juckettd/RaspberryPiCM4Handheld7Inch/Images/IMG_2084.jpg

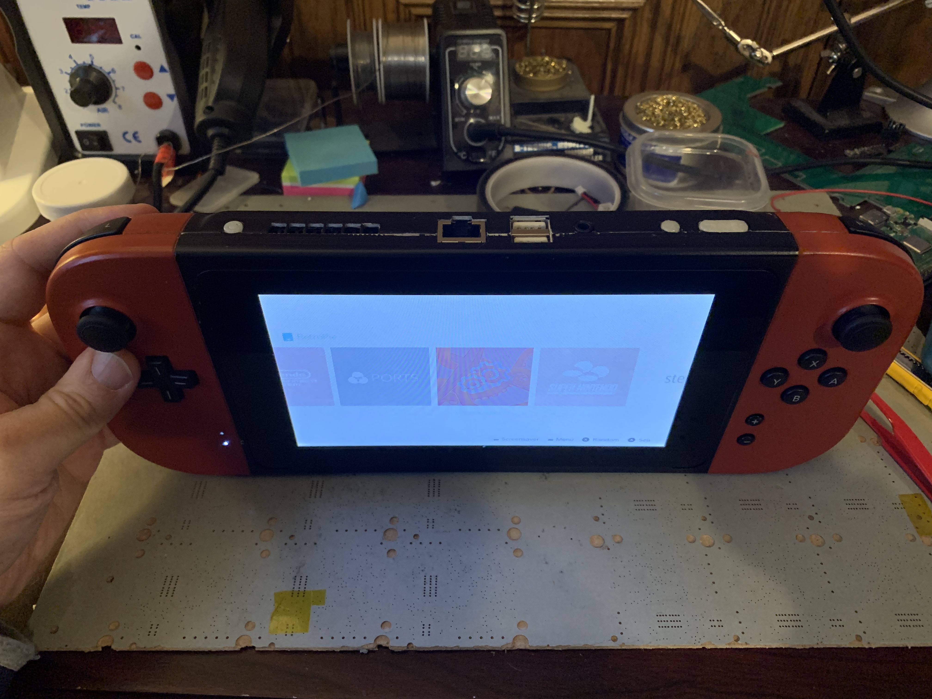
Images/IMG_2084.jpg
