juckettd/RaspberryPiCM4Handheld7Inch/Images/IMG_2085.jpg

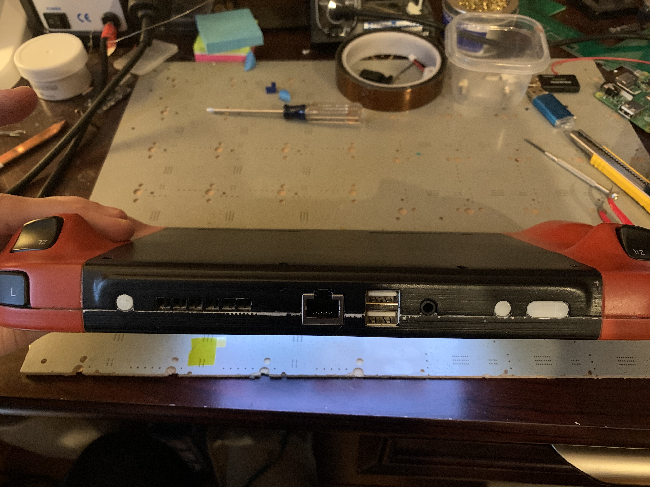
Images/IMG_2085.jpg
