juckettd/RaspberryPiCM4Handheld7Inch/Images/IMG_2086.jpg

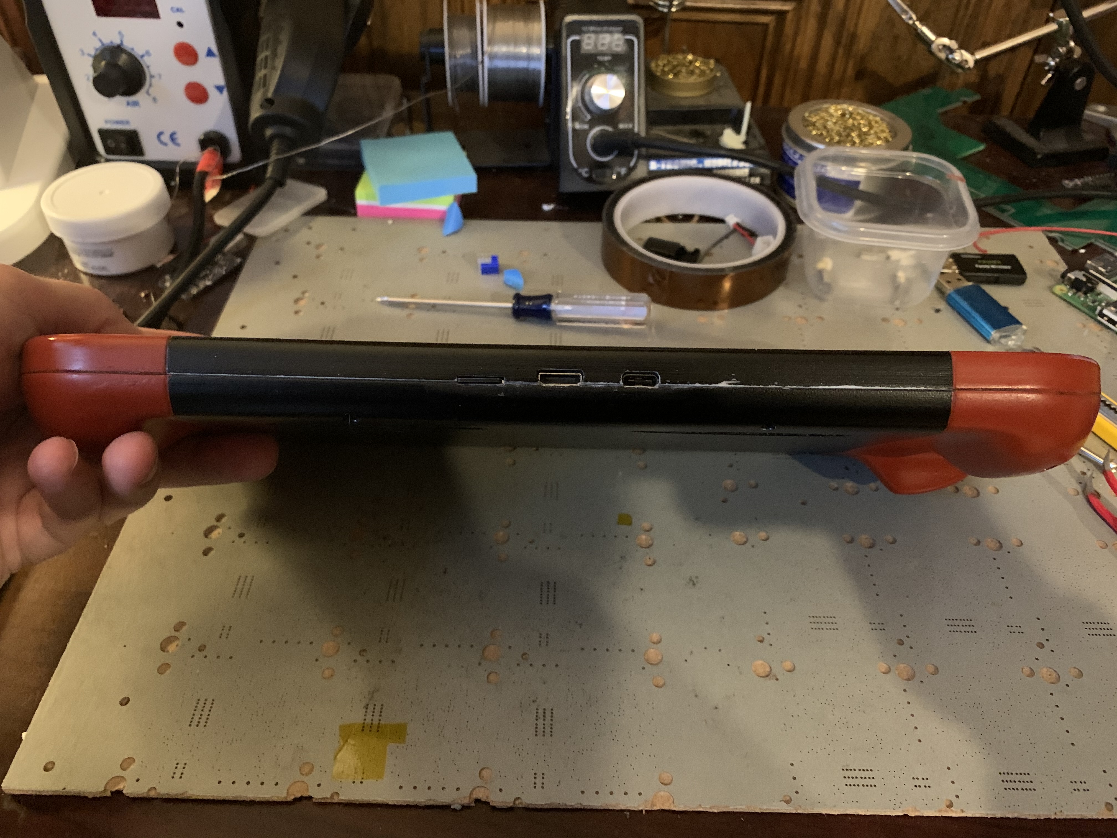
Images/IMG_2086.jpg
