juckettd/RaspberryPiCM4Handheld7Inch/Images/IMG_2087.jpg

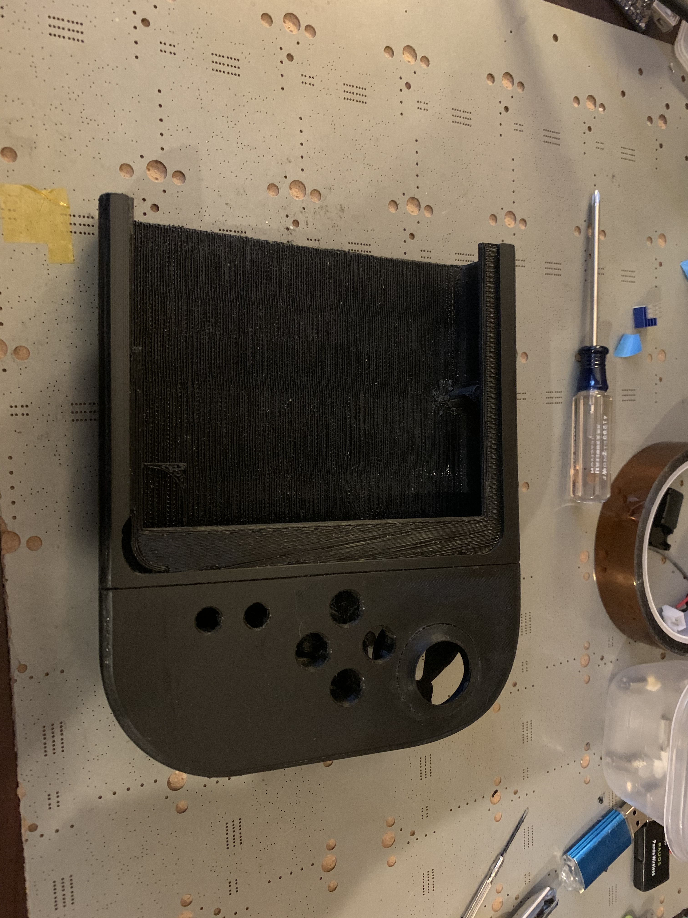
Images/IMG_2087.jpg
