juckettd/RaspberryPiCM4Handheld7Inch/Images/IMG_2089.jpg

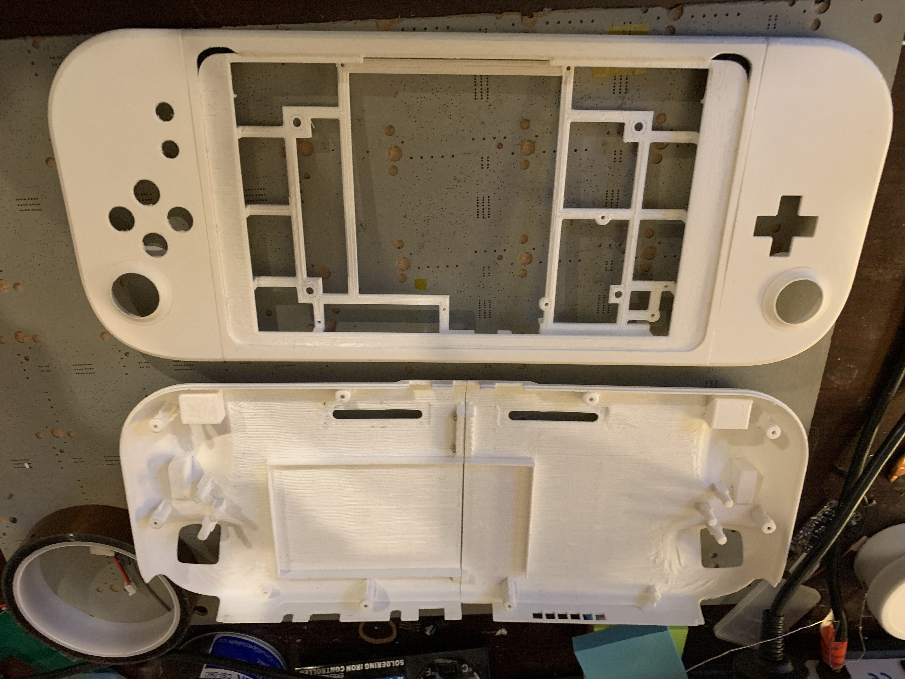
Images/IMG_2089.jpg
