juckettd/RaspberryPiCM4Handheld7Inch/Images/IMG_2090.jpg

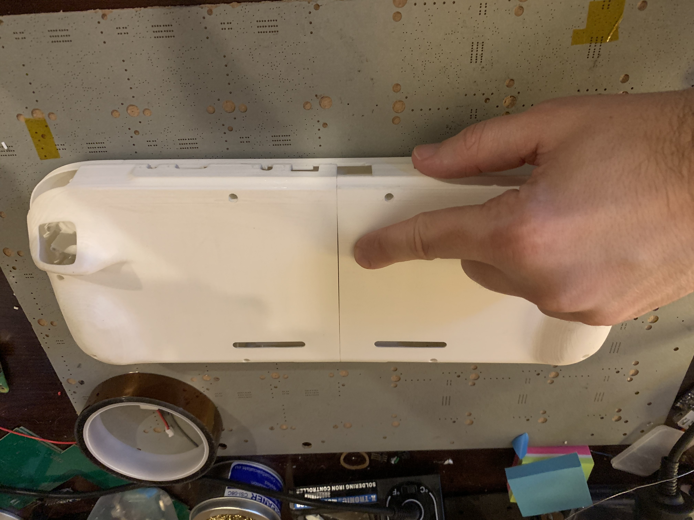
Images/IMG_2090.jpg
