juckettd/RaspberryPiCM4Handheld7Inch/Images/IMG_2092.jpg

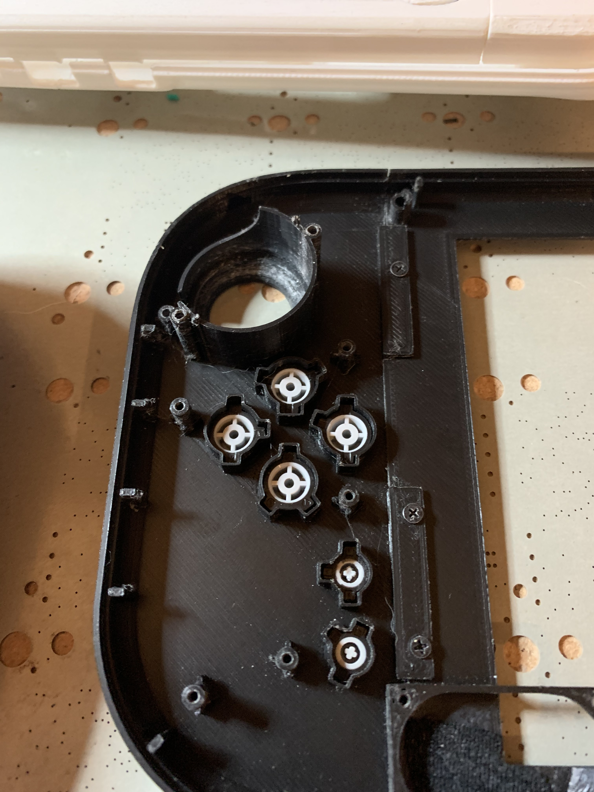
Images/IMG_2092.jpg
