juckettd/RaspberryPiCM4Handheld7Inch/Images/IMG_2093.jpg

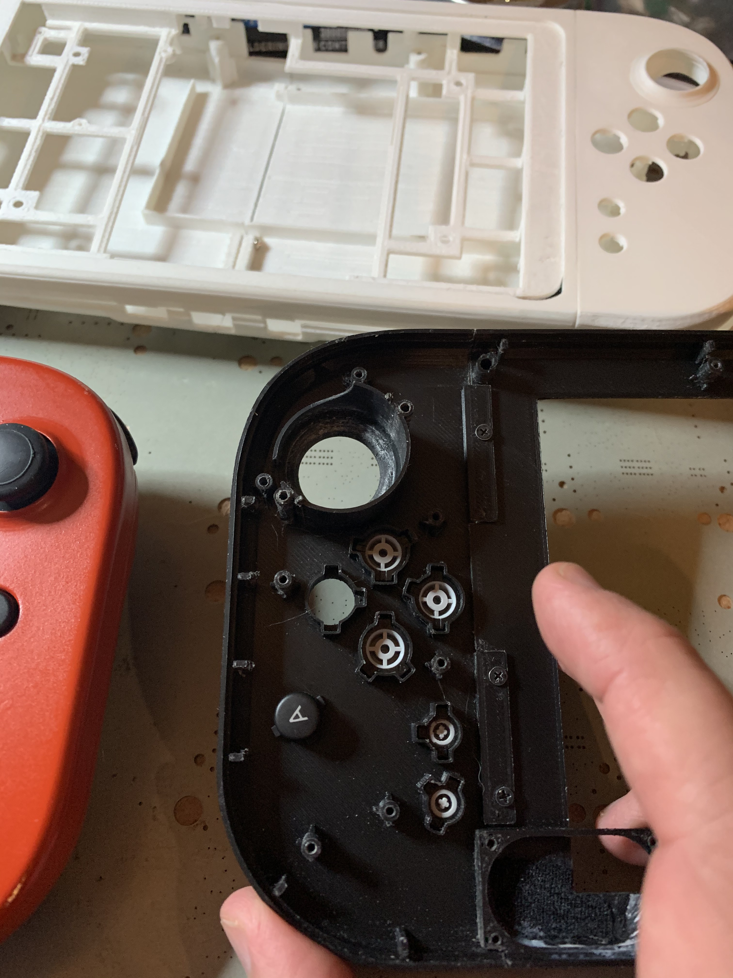
Images/IMG_2093.jpg
