juckettd/RaspberryPiCM4Handheld7Inch/Images/IMG_2094.jpg

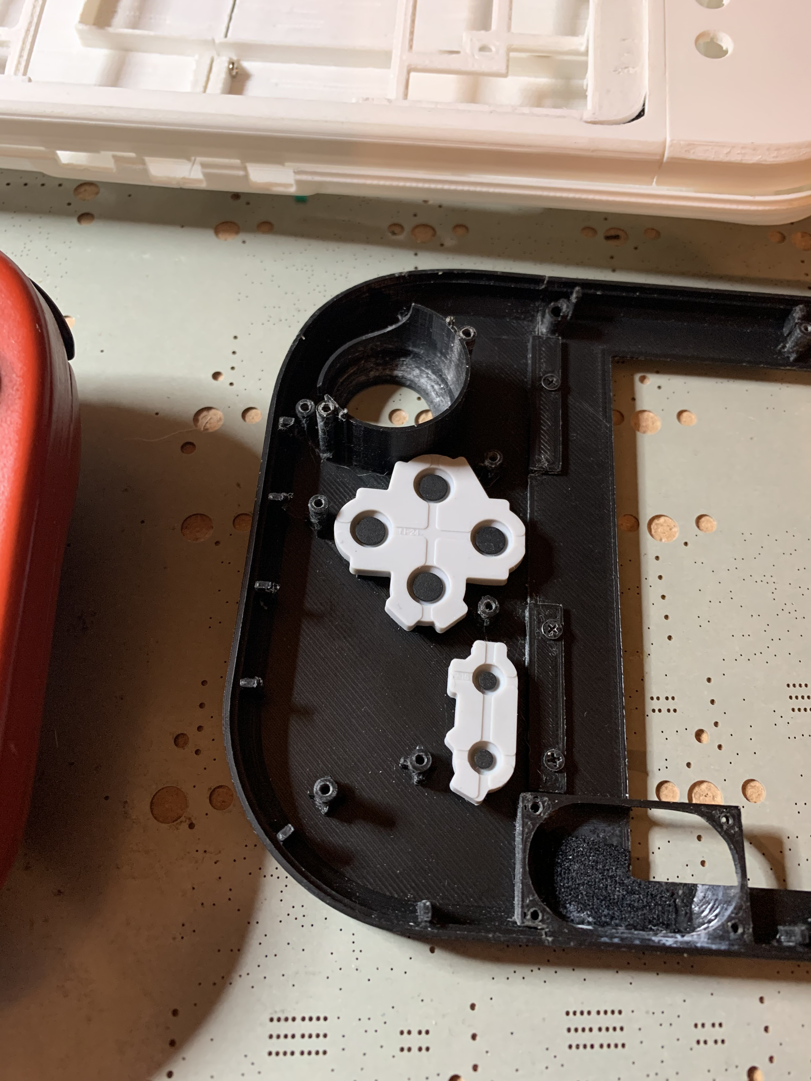
Images/IMG_2094.jpg
