juckettd/RaspberryPiCM4Handheld7Inch/Images/IMG_2095.jpg

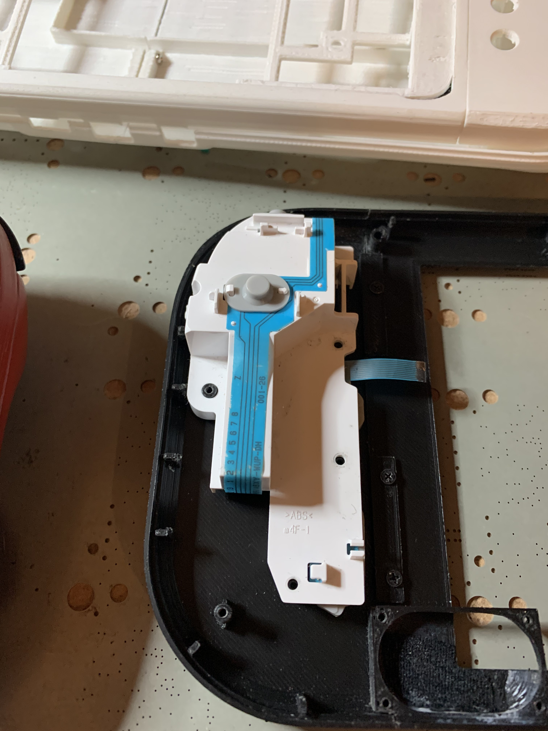
Images/IMG_2095.jpg
