juckettd/RaspberryPiCM4Handheld7Inch/Images/IMG_2096.jpg

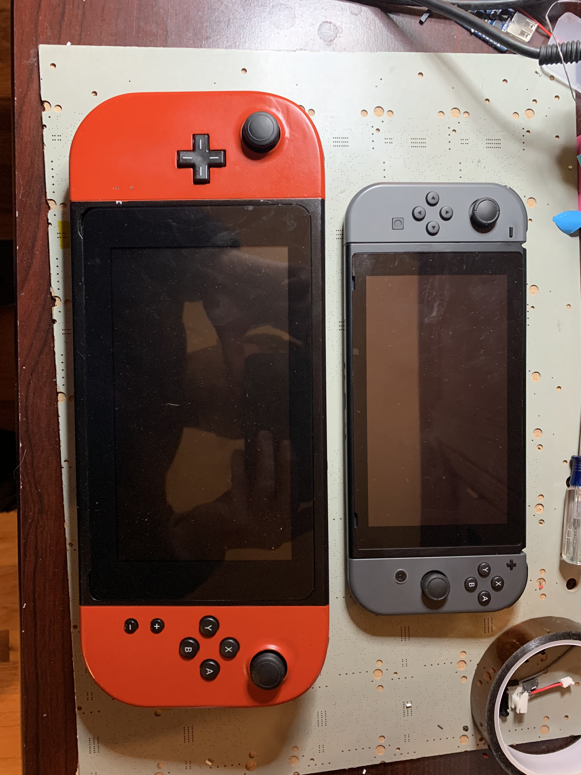
Images/IMG_2096.jpg
