juckettd/RaspberryPiCM4Handheld7Inch/Images/IMG_2108.jpg

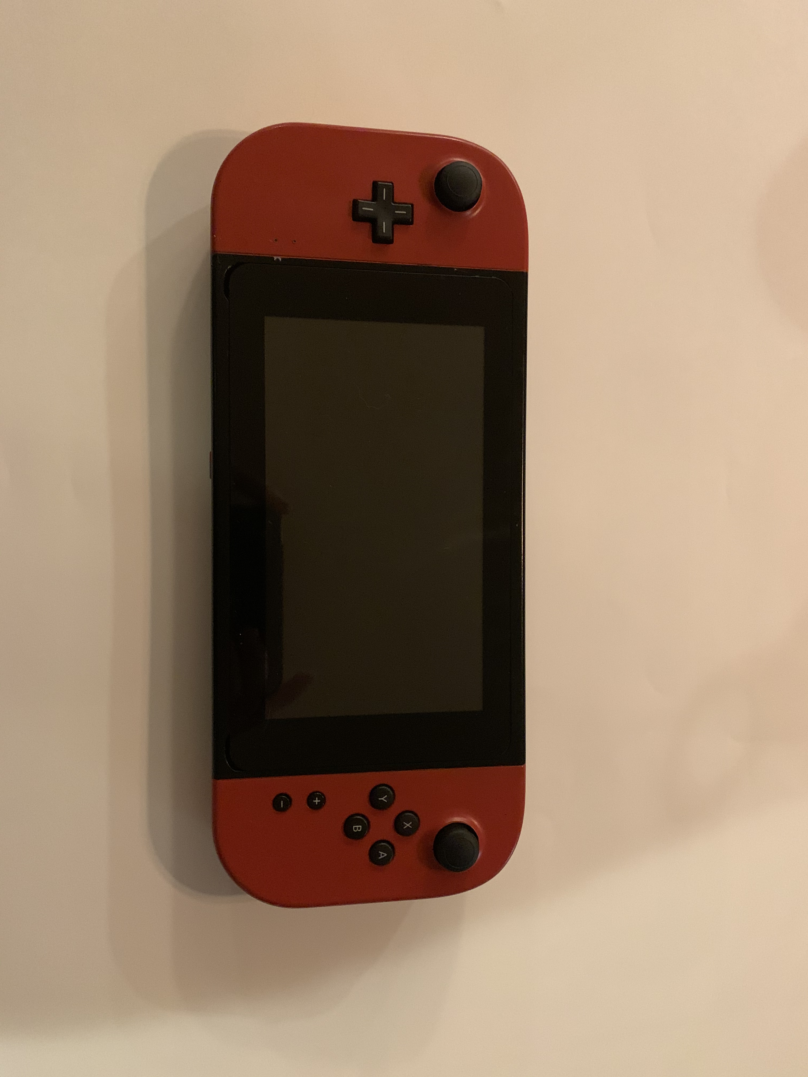
Images/IMG_2108.jpg
