juckettd/RaspberryPiCM4Handheld7Inch/Images/IMG_2109.jpg

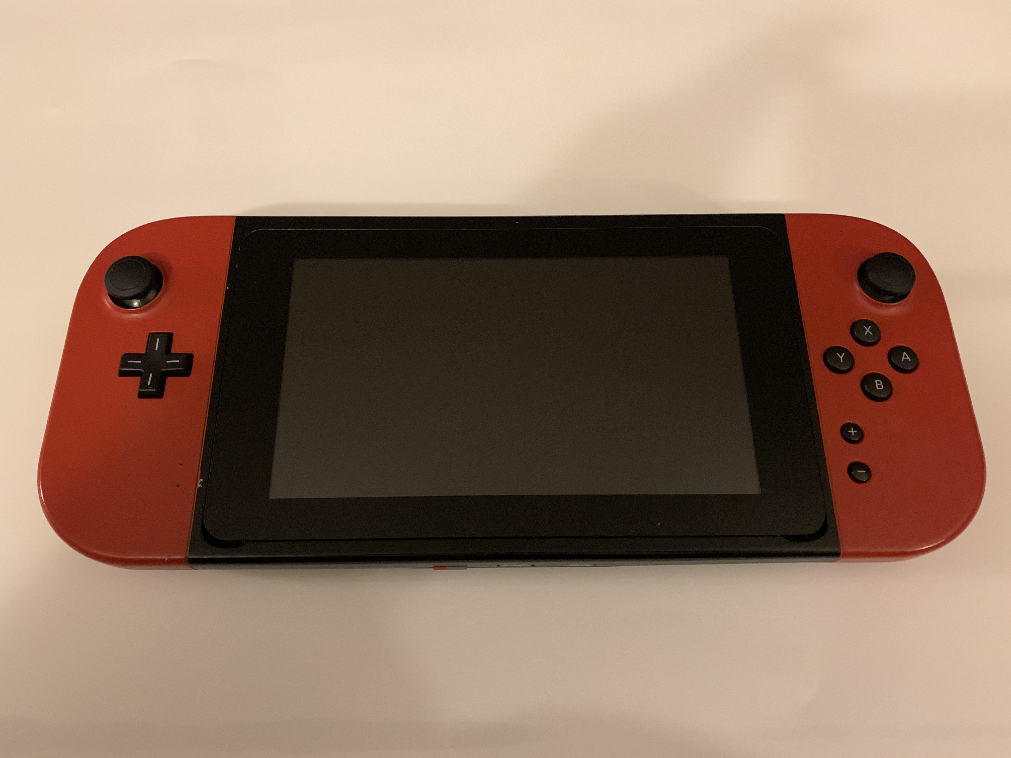
Images/IMG_2109.jpg
