juckettd/RaspberryPiCM4Handheld7Inch/Images/IMG_2110.jpg

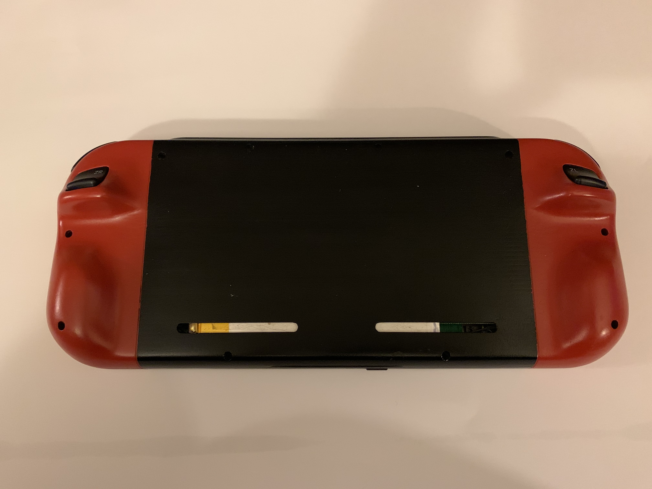
Images/IMG_2110.jpg
