juckettd/RaspberryPiCM4Handheld7Inch/Images/IMG_2111.jpg

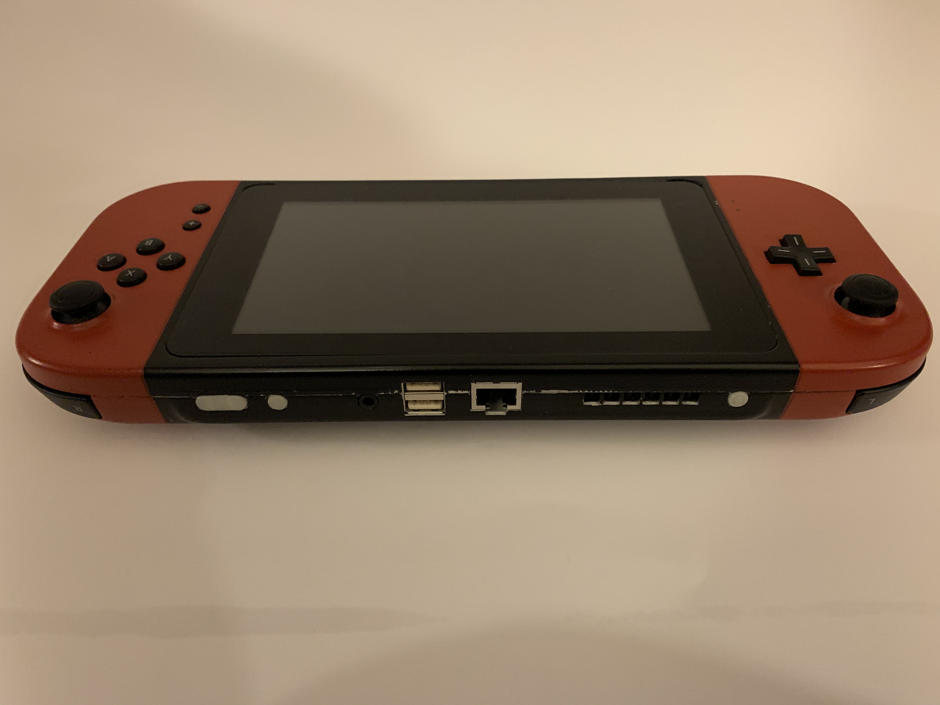
Images/IMG_2111.jpg
