juckettd/RaspberryPiCM4Handheld7Inch/Images/IMG_2112.jpg

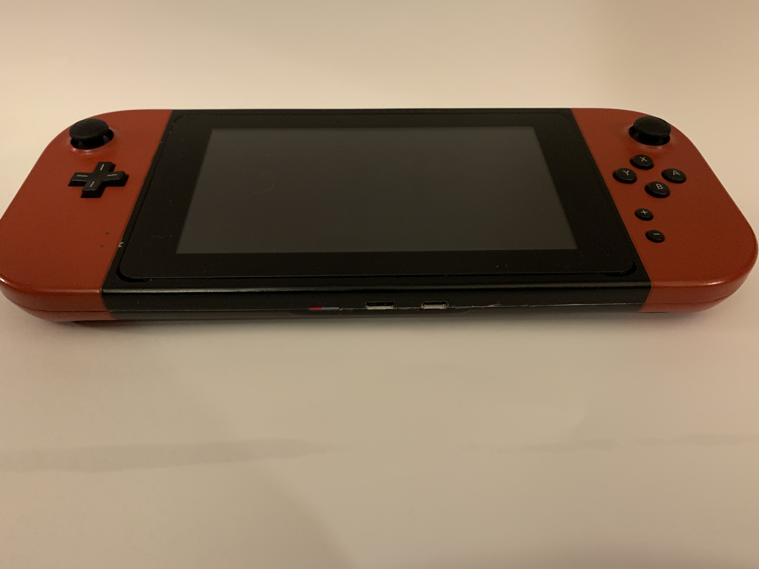
Images/IMG_2112.jpg
