juckettd/RaspberryPiCM4Handheld7Inch/Images/IMG_2113.jpg

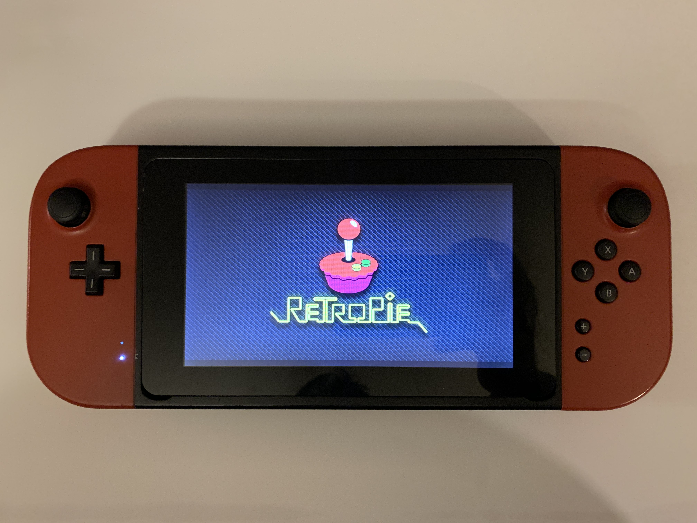
Images/IMG_2113.jpg
