juckettd/RaspberryPiCM4Handheld7Inch/Images/IMG_2115.jpg

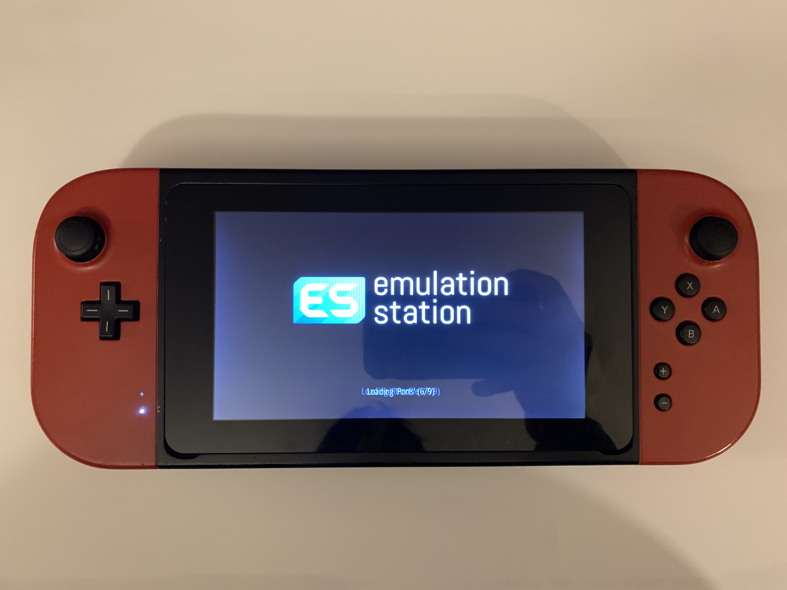
Images/IMG_2115.jpg
