juckettd/RaspberryPiCM4Handheld7Inch/Images/IMG_2079.jpg

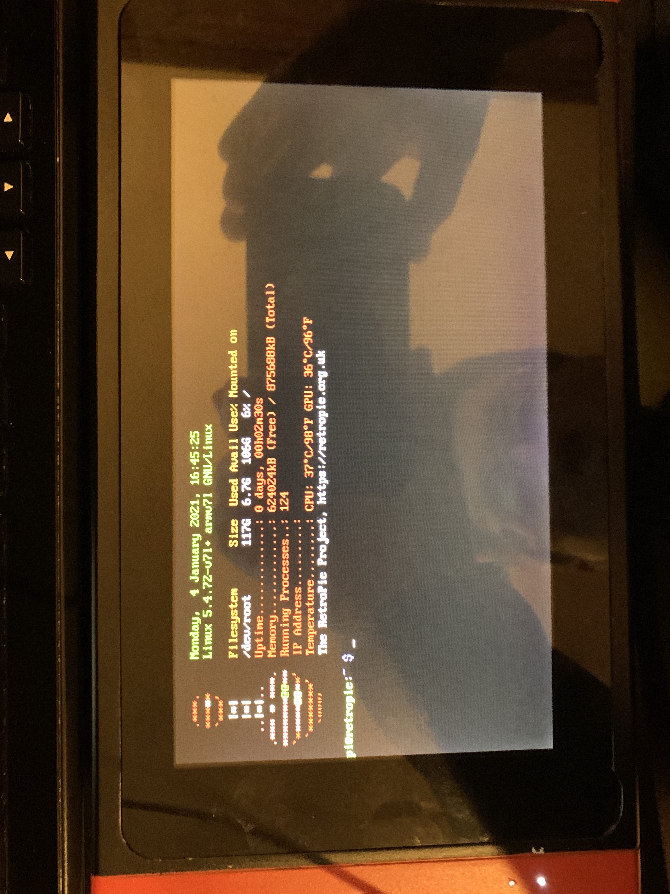
Images/IMG_2079.jpg
