juckettd/RaspberryPiCM4Handheld7Inch/Images/IMG_2080.jpg

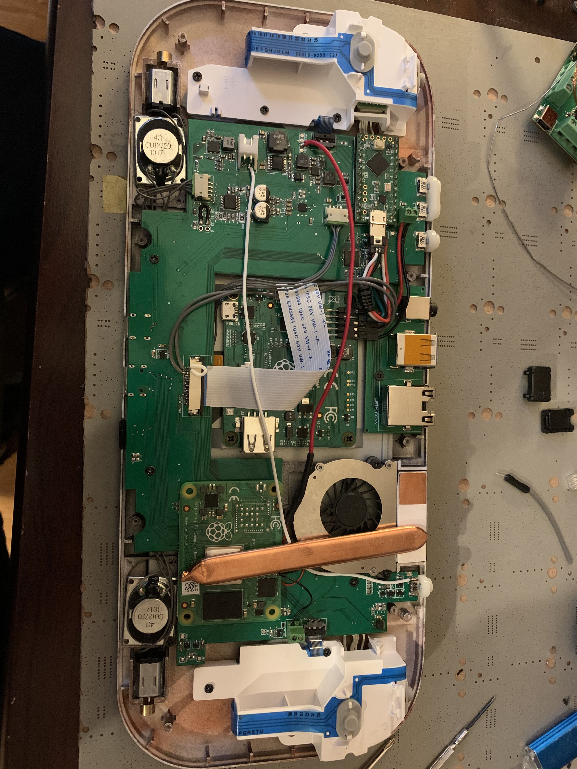
Images/IMG_2080.jpg
