juckettd/RaspberryPiCM4Handheld7Inch/Images/IMG_2081.jpg

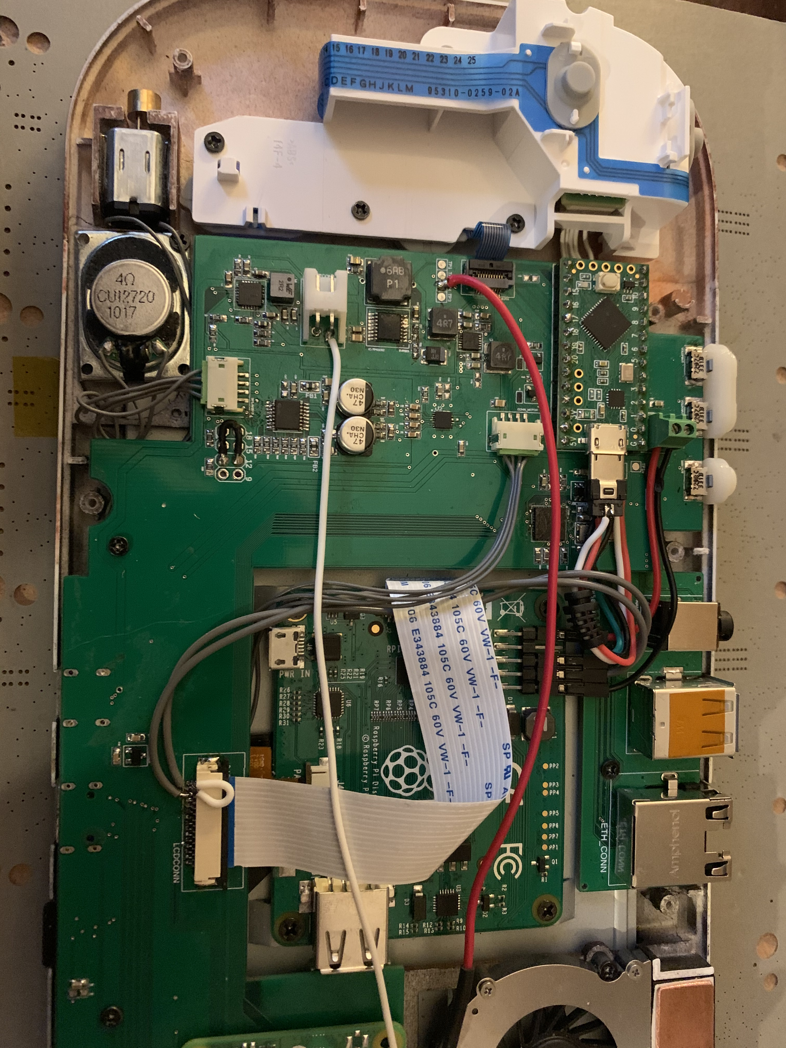
Images/IMG_2081.jpg
