juckettd/RaspberryPiCM4Handheld7Inch/Images/IMG_2082.jpg

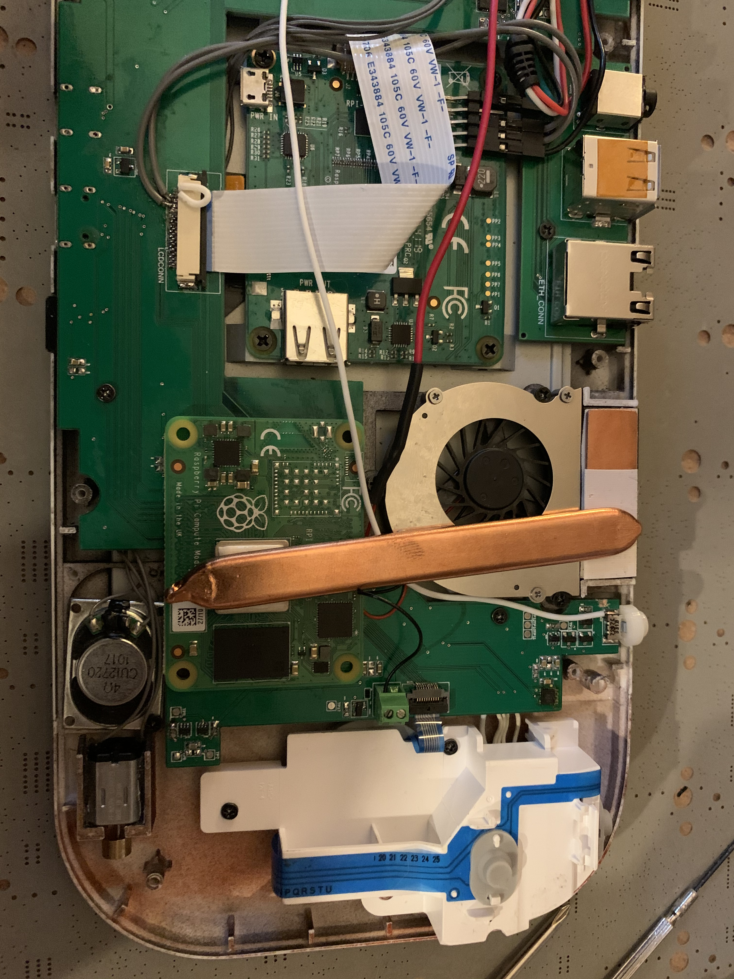
Images/IMG_2082.jpg
