juckettd/RaspberryPiCM4Handheld7Inch/Images/IMG_2083.jpg

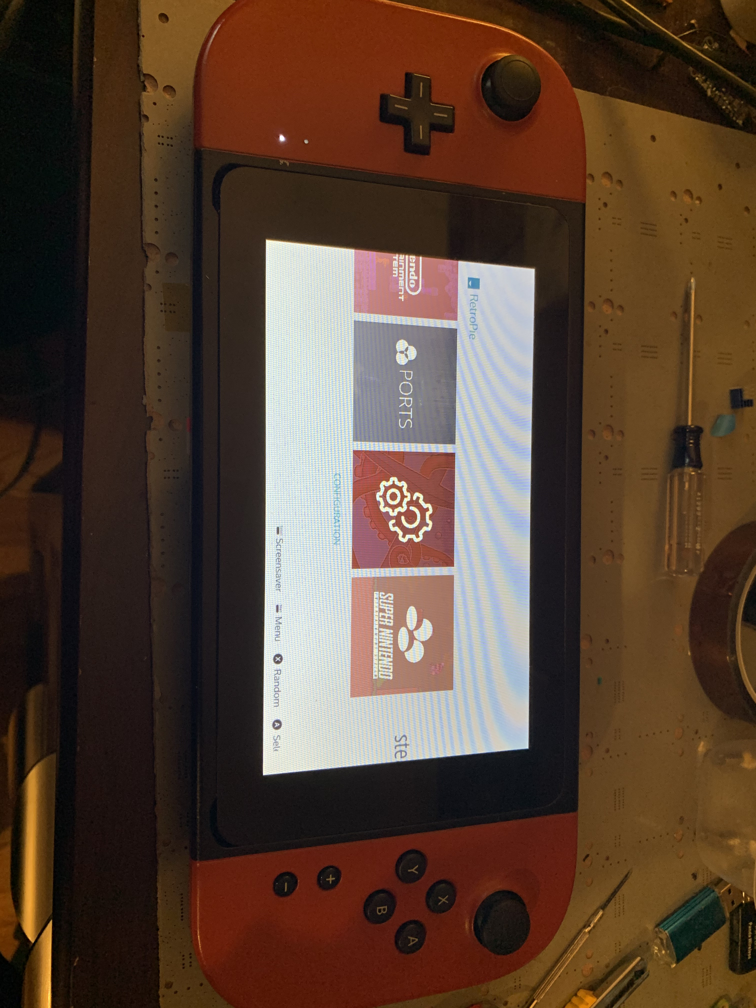
Images/IMG_2083.jpg
