juckettd/RaspberryPiCM4Handheld7Inch/Images/IMG_2088.jpg

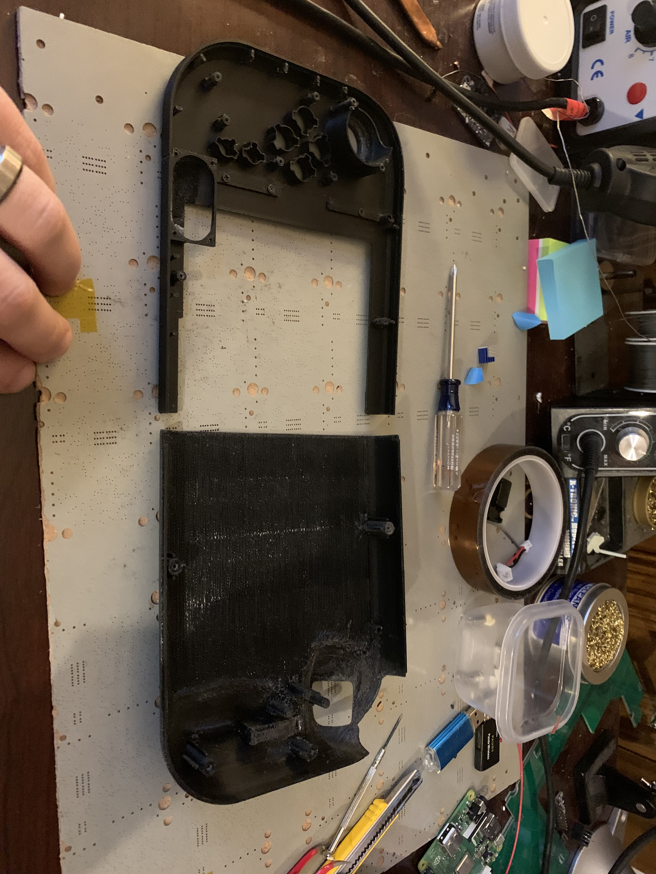
Images/IMG_2088.jpg
